MyRetroStore/RetroRomTester/software/Arduino/crc.h

struct t_md5_8192 {
  char fileName[32];
  char hash1[33];
  char hash2[33];
};

struct t_md5_4096 {
  char fileName[32];
  char hash1[33];
};

static const t_md5_8192 md5_8192[] PROGMEM = {
  {"basic_901226_01", "ef209f5b3d59a878a9be73eb254aa429", "bc16916b5f8f5eabf25cfadb97cf0499"},
  {"kernal_901486_07", "8eb34bdcce4b66a6f3ef249ae2977a9a", "4583fdffdefe05379c6b047ab84faebb"},
  {"kernal_901227_01", "4acf4124d215b8f7dd58cf1f9fca2b14", "3a83704039416658e3f4c602d7495bde"},
  {"kernal_901486_06", "2426f8737d5fe275a09d4dcca2ea481a", "dad200bdf2ced3b2f837a829796e2f5b"},
  {"kernal_sx_251104_04", "956e0c60af9896e3b47da1eeab4a208a", "123fb81696dcae26b30105ba6291fb79"},
  {"kernal_901227_03", "e4028272f6d0cd7b10c8500c435ef7d6", "b2db908d3c6272992fad616287234310"},
  {"kernal_901227_02", "aac13be6cefbac706f718d1663ccd303", "c393ac15f5389696033f5d744b3908d7"},
  {"basic_901486_01", "29884822dc17398316af2c0f67c633d6", "fe2c56e9e957cea39cd25a806aa6e53f"},
  {"64er_v1", "b3662a475cd37bff0f71ed1b08fd4914", "46cb495a2536795c2f1a246412750405"},
  {"deadtest_781220", "5cec2519ed8cac5d375ac86f772797e5", "0ab1eae738a817f74c3d23e6c484f813"},
  {"dolphindos_v2", "b949247bd4c07d9f7ad512285300dfb8", "e01283fe662fb836ea4e57d94d5e4256"},
  {"memostar", "674e594d7338bc0b18e2f1cf3edc8632", "a15a1cc6543be4dcf2fc85854773e44b"},
  {"turbodos_v3", "6fad4183669c358fd2258ed4e374df2f", "4f27ae69174e87199de242cd8721ae34"},  
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
  {"rom_1_c800_901439_05", "d03ee896c37ad1bd86773655948e1174"},
  {"rom_3_e000_901447_24", "cb8e8404c0b28eda10469792dfd1dbc2"},
  {"edit_4_80_b_50Hz_901474_04_alt", "6f6d732cc4376a3514d0e6e6e0b24d96"},
  {"rom_3_c000_901447_20", "a271c2b8ba70a6d4dddb2a05f69dc700"},
  {"rom_2_c000_901439_09", "9eaf58aa938083ad74117a81ac460e37"},
  {"edit_2_n_901447_24", "cb8e8404c0b28eda10469792dfd1dbc2"},
  {"characters_2_901447_10", "9880432e633b15998d58884ff34c4e70"},
  {"rom_3_f800_901439_19", "9e75c9b9002016e9623466314c3907ed"},
  {"rom_3_c800_901447_21", "3df7df239614d8bc3bd0d57e203891af"},
  {"rom_1_d800_901447_04", "673b61a8fe11cd5d7e4003f81a2d8453"},
  {"rom_1_f000_901439_04", "2d44afcab9713ad4d11118a9e7429a81"},
  {"rom_3_f800_901447_26", "9e75c9b9002016e9623466314c3907ed"},
  {"rom_2_c000_901447_09", "9eaf58aa938083ad74117a81ac460e37"},
  {"rom_3_d800_901447_23", "b46faf112d94ef9b90c5c38acc365114"},
}; // End of 4k marker
